sssata/HYKU/CAD/cad exports/008 UPPER ARM PCB2.DXF

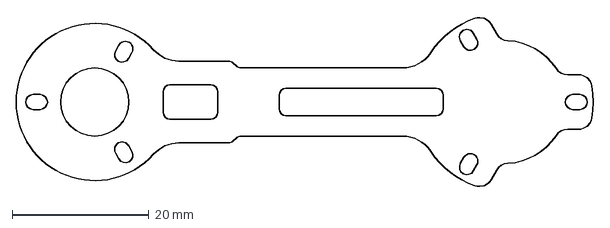
[picture p23: CAD file, 2021-12-31]
CAD/cad exports/008 UPPER ARM PCB2.DXF
84.6 x 25.1 mm
