sssata/HYKU/CAD/imported/Cherry MX Pins.SLDPRT

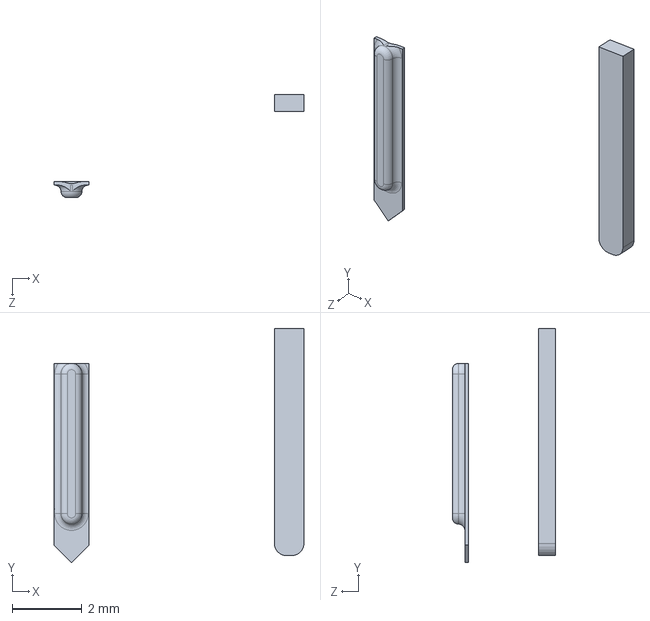
[picture p24: CAD file, 2021-12-25]
CAD/imported/Cherry MX Pins.SLDPRT
7.15 x 6.70 x 2.96 mm
