sssata/HYKU/CAD/006 BEARING MALE PLATE.SLDPRT

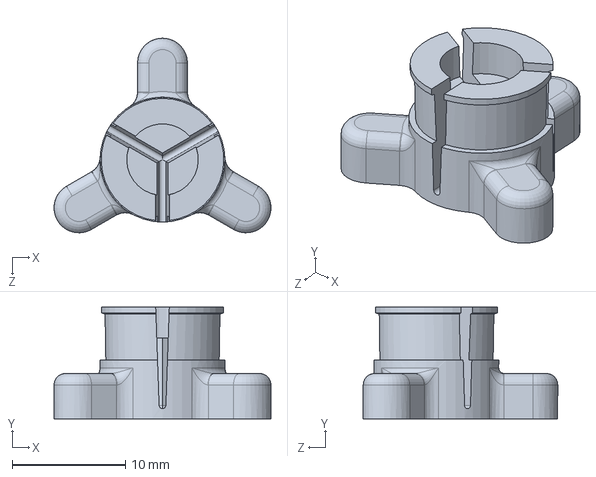
[picture p25: CAD file, 2022-01-21]
CAD/006 BEARING MALE PLATE.SLDPRT
19.1 x 9.85 x 17.2 mm
