sssata/HYKU/CAD/016 LOWER ARM PCB.SLDPRT

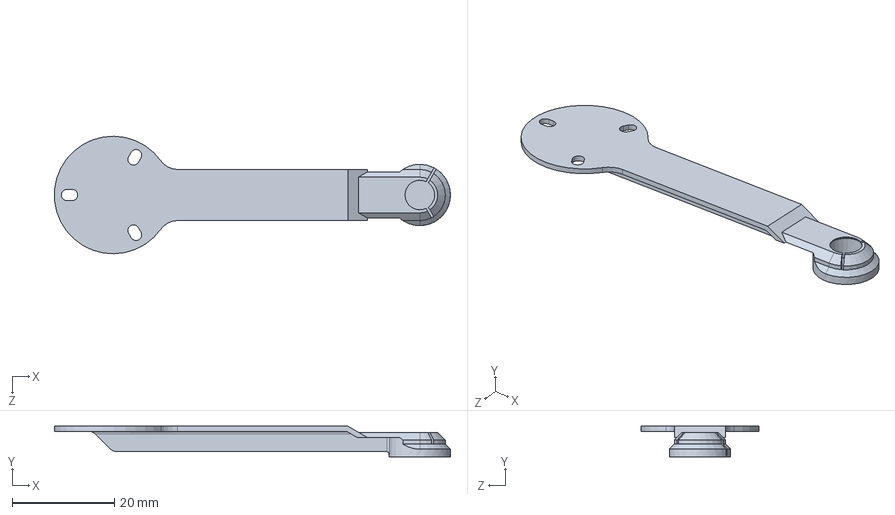
[picture p26: CAD file, 2022-01-21]
CAD/016 LOWER ARM PCB.SLDPRT
77.4 x 6.00 x 23.0 mm
