sssata/HYKU/CAD/imported/Cherry MX Stem.SLDPRT

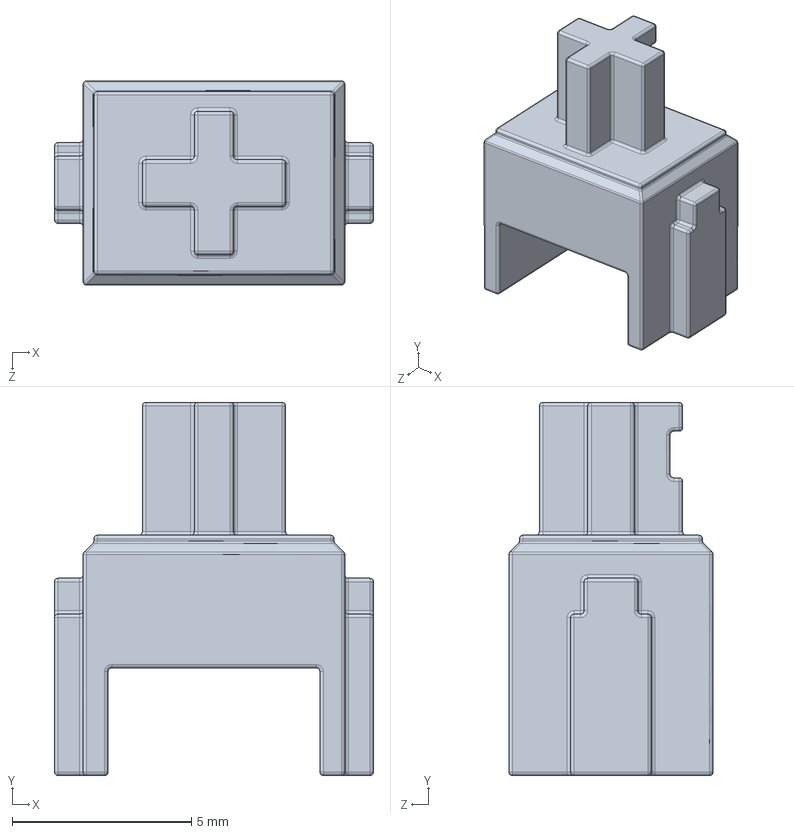
[picture p27: CAD file, 2021-12-25]
CAD/imported/Cherry MX Stem.SLDPRT
8.90 x 10.4 x 5.70 mm
