sssata/HYKU/CAD/imported/Cherry MX Top Housing.SLDPRT

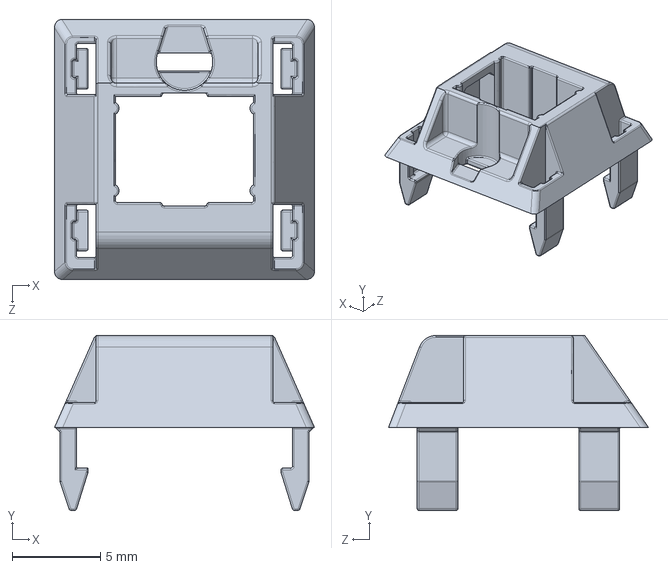
[picture p28: CAD file, 2021-12-25]
CAD/imported/Cherry MX Top Housing.SLDPRT
14.7 x 9.90 x 14.7 mm
