sssata/HYKU/CAD/008 UPPER ARM PCB.SLDPRT

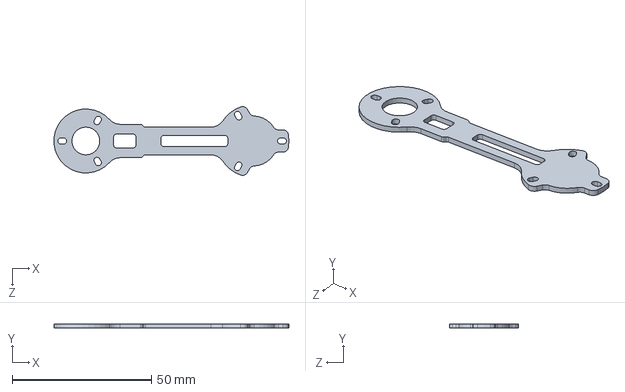
[picture p29: CAD file, 2021-12-31]
CAD/008 UPPER ARM PCB.SLDPRT
84.4 x 1.60 x 24.7 mm
