sssata/HYKU/CAD/imported/Cherry MX LED.SLDPRT

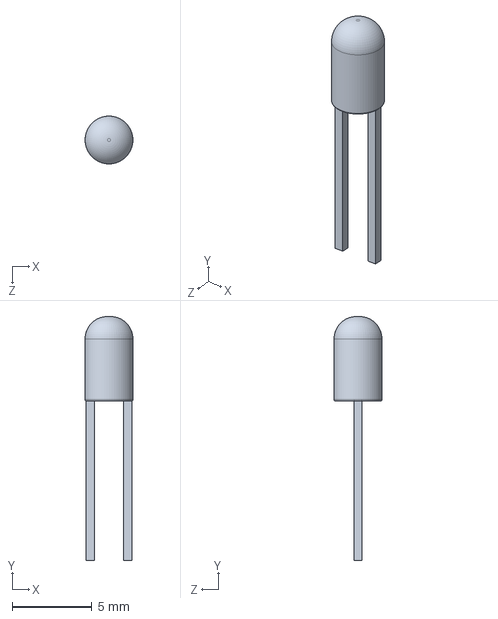
[picture p30: CAD file, 2021-12-25]
CAD/imported/Cherry MX LED.SLDPRT
3.00 x 15.3 x 3.00 mm
