sssata/HYKU/CAD/022 PEN NIB.SLDPRT

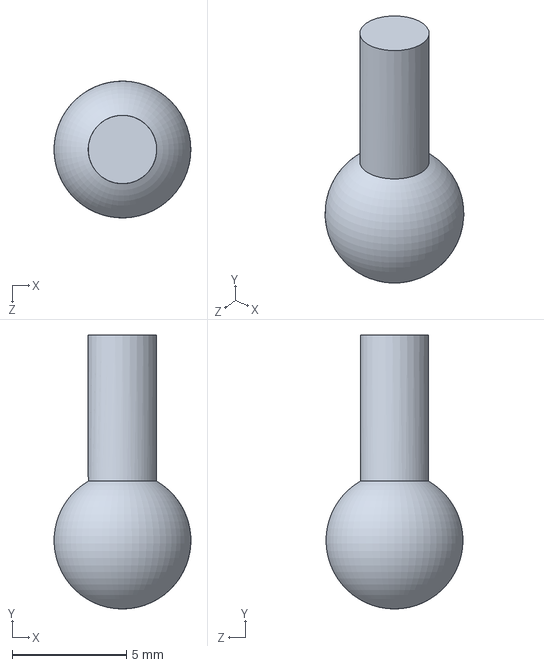
[picture p31: CAD file, 2021-12-31]
CAD/022 PEN NIB.SLDPRT
5.99 x 12.0 x 5.99 mm
