sssata/HYKU/CAD/010 BASE KICAD EXP.SLDPRT

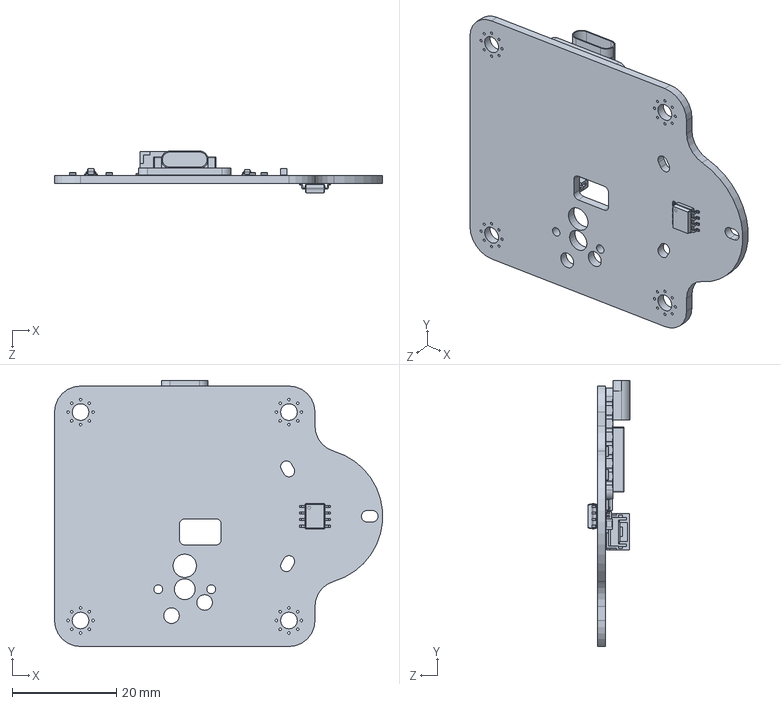
[picture p32: CAD file, 2021-12-31]
CAD/010 BASE KICAD EXP.SLDPRT
63.0 x 51.1 x 8.05 mm
