sssata/HYKU/CAD/013 AS5600 SOIC-8.SLDPRT

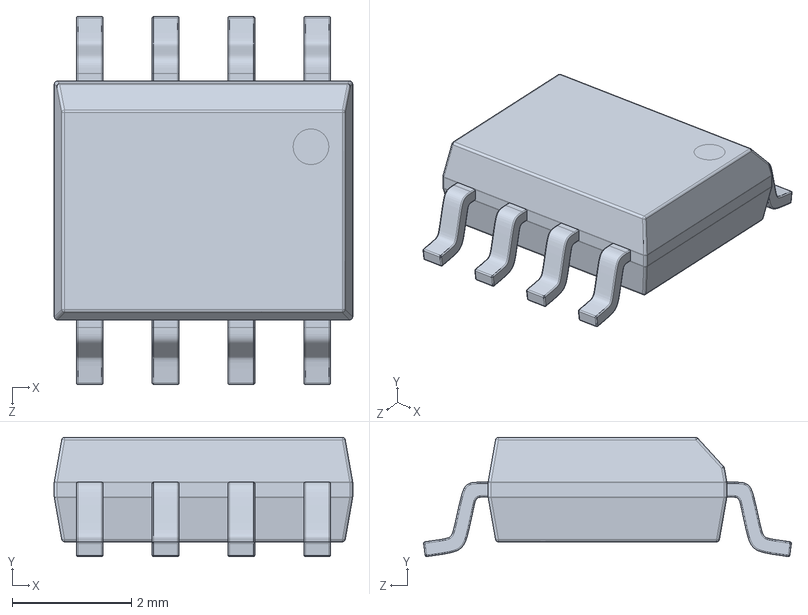
[picture p33: CAD file, 2021-12-31]
CAD/013 AS5600 SOIC-8.SLDPRT
5.00 x 2.00 x 6.16 mm
