sssata/HYKU/CAD/005 BEARING FEMALE PLATE.SLDPRT

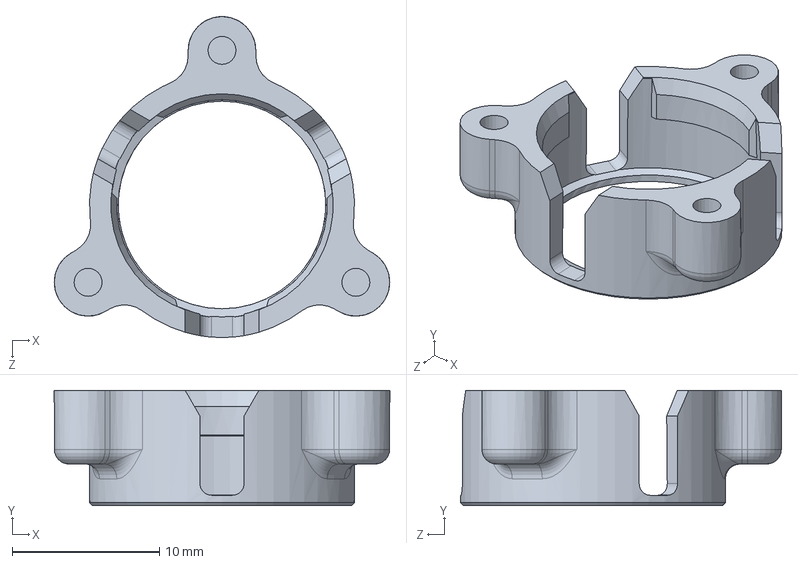
[picture p34: CAD file, 2021-12-31]
CAD/005 BEARING FEMALE PLATE.SLDPRT
22.8 x 7.82 x 21.8 mm
