sssata/HYKU/CAD/009 6x2mm MAGNET.SLDPRT

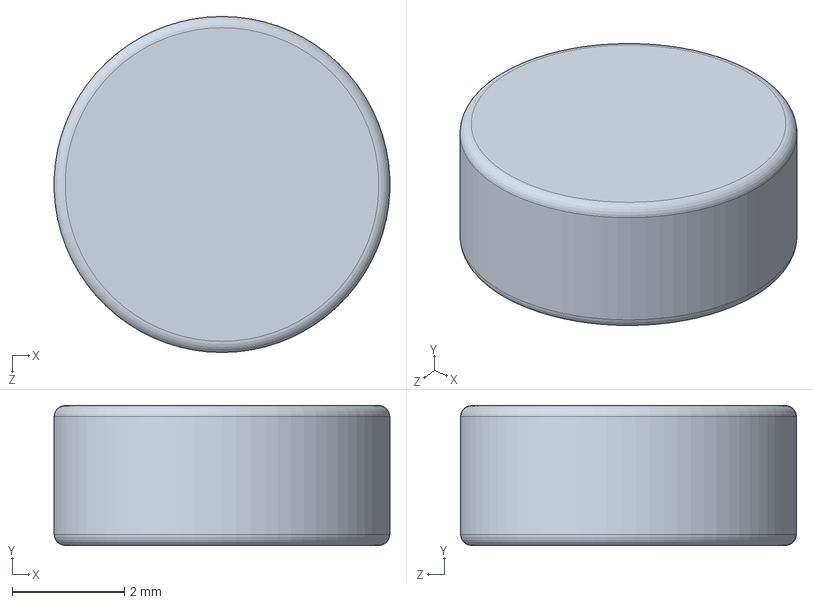
[picture p35: CAD file, 2021-12-31]
CAD/009 6x2mm MAGNET.SLDPRT
5.99 x 2.50 x 6.00 mm
