sssata/HYKU/CAD/017 AREA PCB.SLDPRT

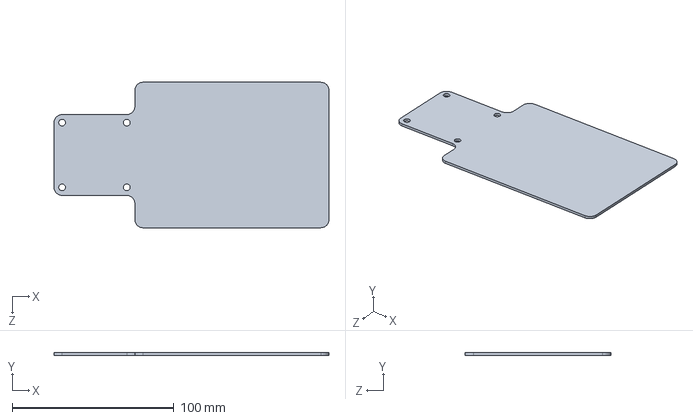
[picture p36: CAD file, 2021-12-25]
CAD/017 AREA PCB.SLDPRT
170.0 x 1.60 x 90.0 mm
