sssata/HYKU/CAD/003 LOWER ARM REV2.SLDPRT

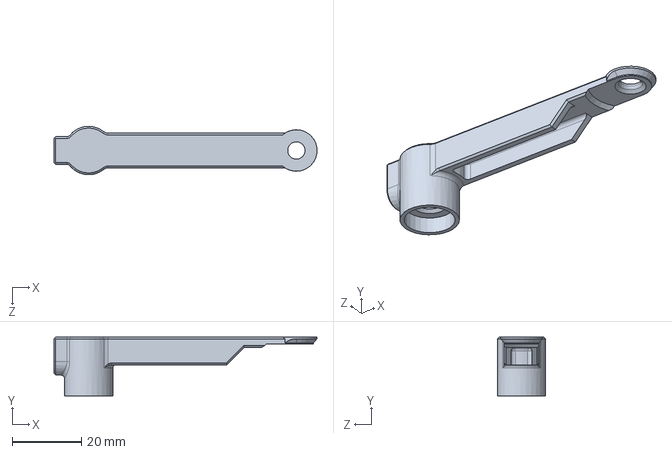
[picture p37: CAD file, 2021-12-25]
CAD/003 LOWER ARM REV2.SLDPRT
76.0 x 17.0 x 14.0 mm
