sssata/HYKU/CAD/015 JST NSH 5 PIN WIRE SIDE.SLDPRT

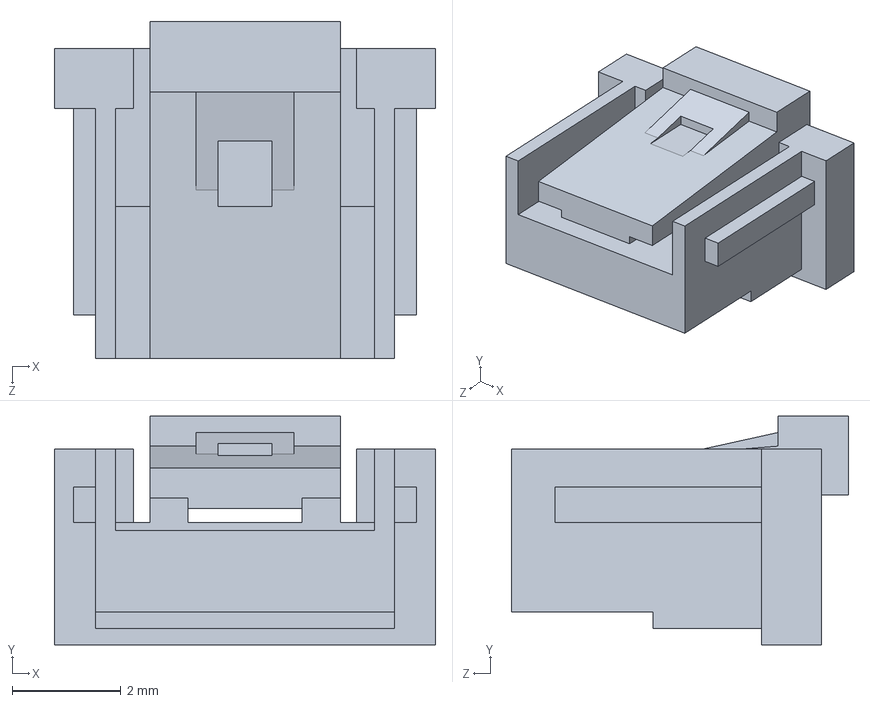
[picture p38: CAD file, 2021-12-25]
CAD/015 JST NSH 5 PIN WIRE SIDE.SLDPRT
7.00 x 4.20 x 6.20 mm
