sssata/HYKU/CAD/002 UPPER ARM REV2.SLDPRT

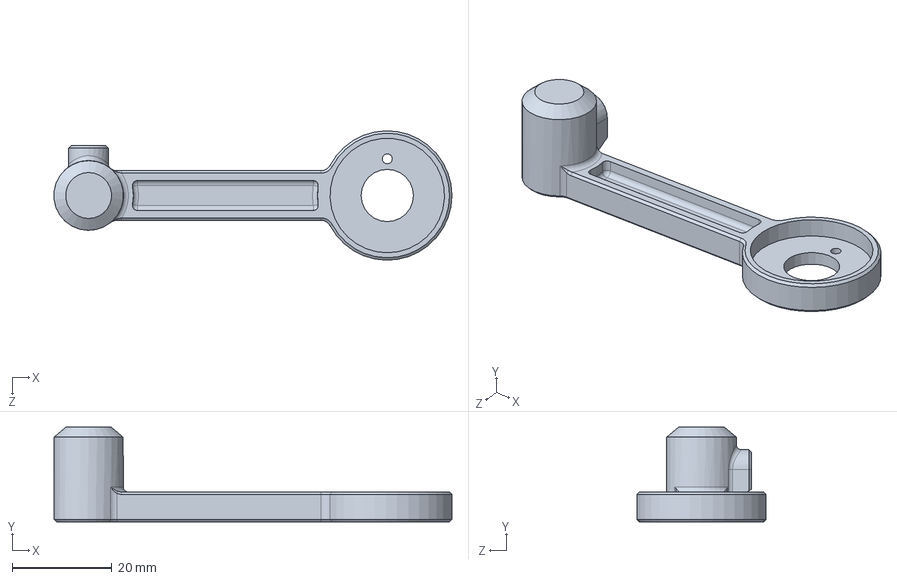
[picture p39: CAD file, 2021-12-25]
CAD/002 UPPER ARM REV2.SLDPRT
80.0 x 19.0 x 26.0 mm
