sssata/HYKU/CAD/001 BASE REV2.SLDPRT

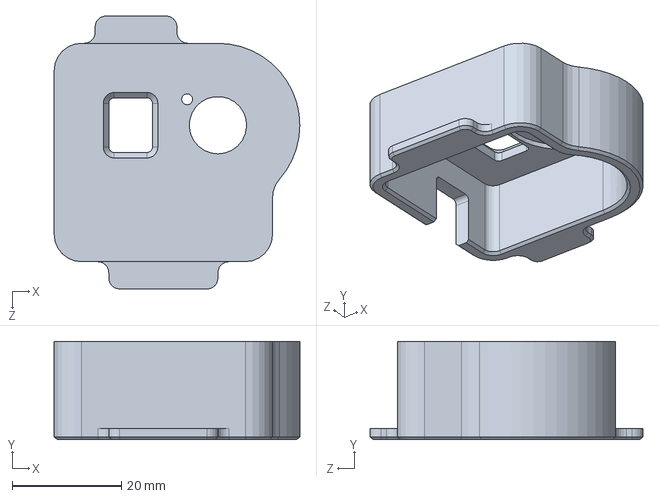
[picture p40: CAD file, 2021-12-25]
CAD/001 BASE REV2.SLDPRT
45.0 x 18.0 x 50.0 mm
