sssata/HYKU/CAD/007 6700ZZ bearing.SLDPRT

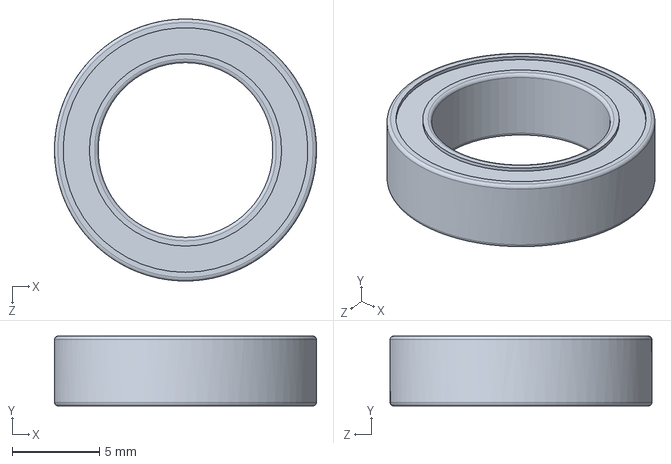
[picture p41: CAD file, 2021-12-25]
CAD/007 6700ZZ bearing.SLDPRT
15.0 x 4.00 x 15.0 mm
