sssata/HYKU/CAD/010 BASE.SLDPRT

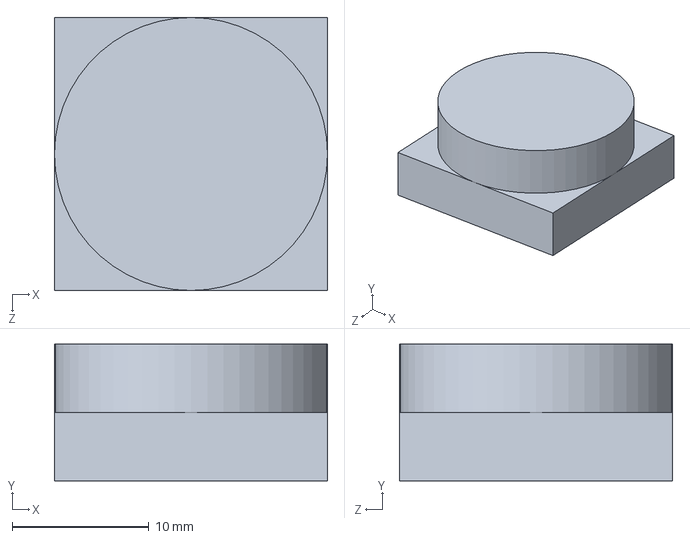
[picture p42: CAD file, 2021-12-25]
CAD/010 BASE.SLDPRT
20.0 x 10.0 x 20.0 mm
