sssata/HYKU/CAD/012 SeeeduinoXiao3D.SLDPRT

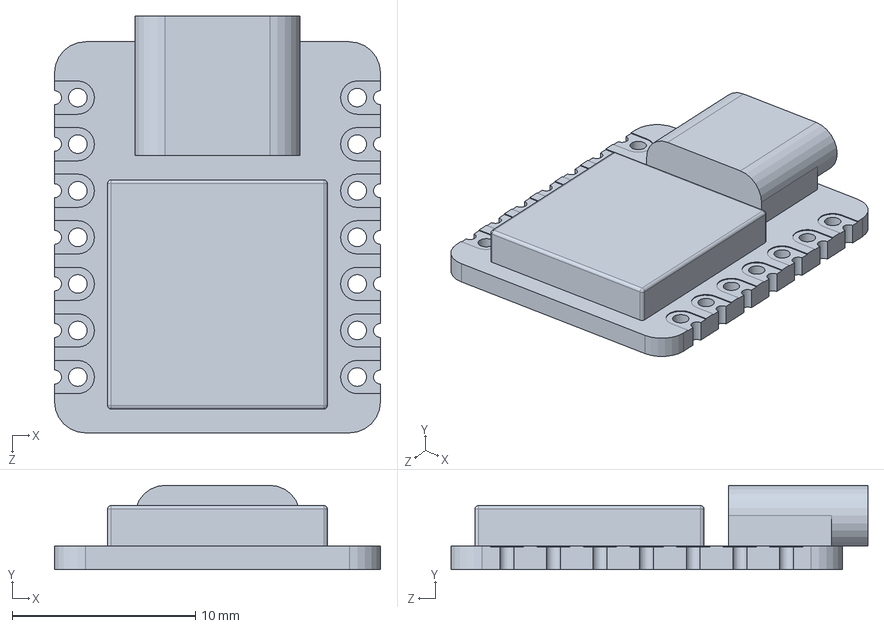
[picture p43: CAD file, 2021-12-25]
CAD/012 SeeeduinoXiao3D.SLDPRT
17.8 x 4.60 x 22.7 mm
