sssata/HYKU/CAD/004 MR85ZZ bearing.SLDPRT

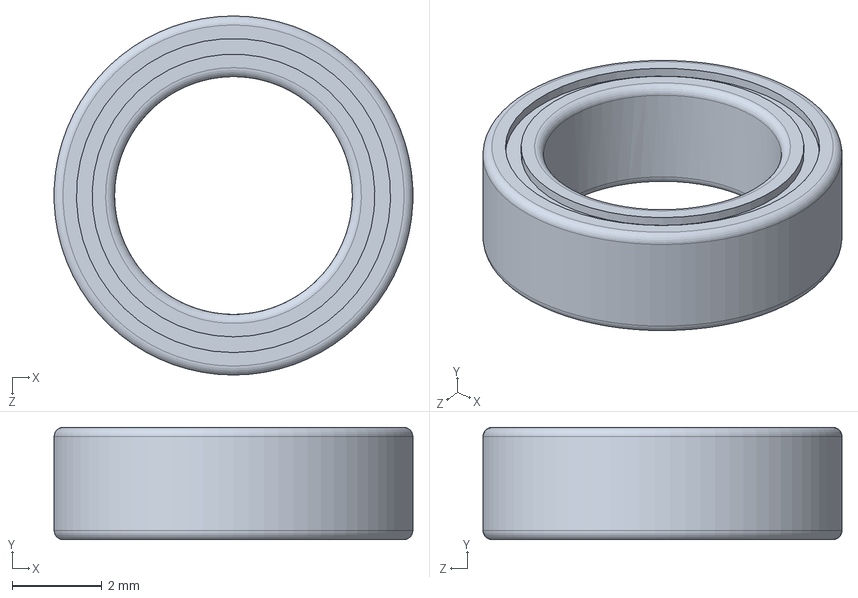
[picture p44: CAD file, 2021-12-25]
CAD/004 MR85ZZ bearing.SLDPRT
7.99 x 2.50 x 8.00 mm
