sssata/HYKU/CAD/011 BASE PCB.SLDPRT

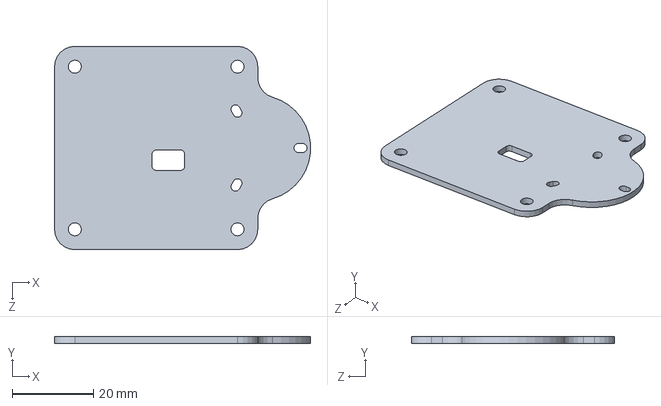
[picture p45: CAD file, 2021-12-25]
CAD/011 BASE PCB.SLDPRT
63.0 x 1.60 x 50.0 mm
