sssata/HYKU/CAD/020 STANDOFF 3x6.SLDPRT

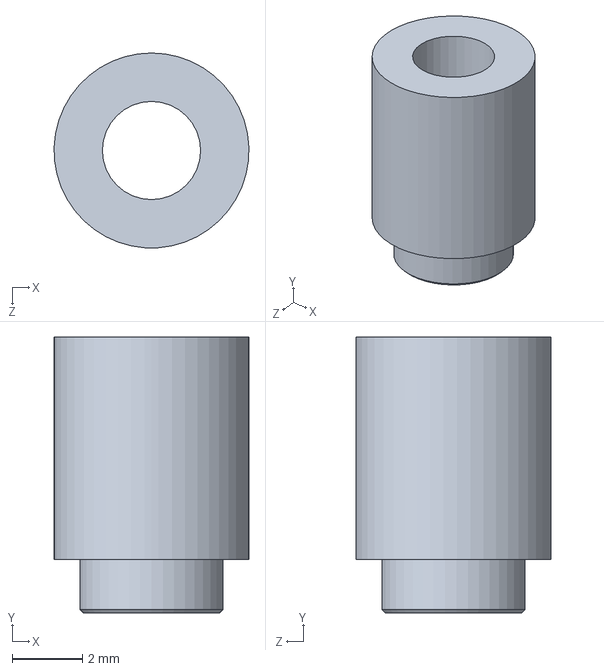
[picture p46: CAD file, 2021-12-25]
CAD/020 STANDOFF 3x6.SLDPRT
5.56 x 7.87 x 5.56 mm
