sssata/HYKU/CAD/019.SLDPRT

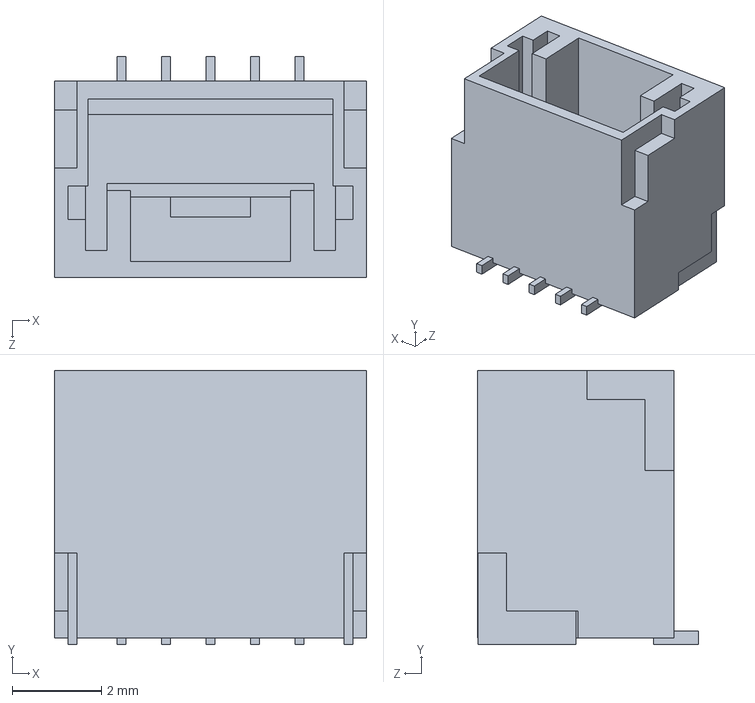
[picture p47: CAD file, 2021-12-25]
CAD/019.SLDPRT
7.00 x 6.15 x 4.95 mm
