sssata/HYKU/CAD/014 JST NSH 5 PIN BOARD SIDE.SLDPRT

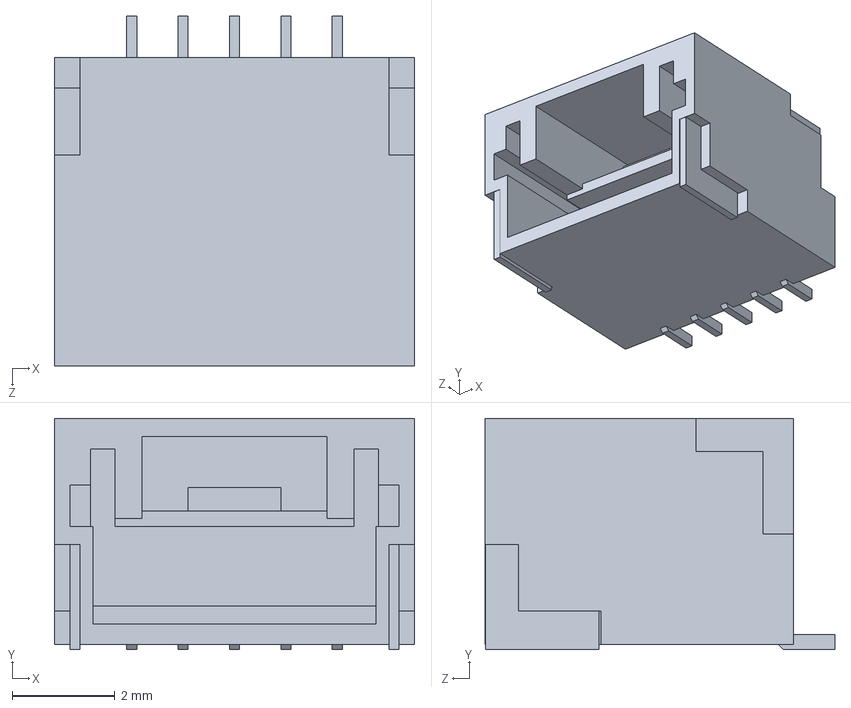
[picture p48: CAD file, 2021-12-25]
CAD/014 JST NSH 5 PIN BOARD SIDE.SLDPRT
7.00 x 4.50 x 6.80 mm
