sssata/HYKU/CAD/020 JST NSH CRIMP.SLDPRT

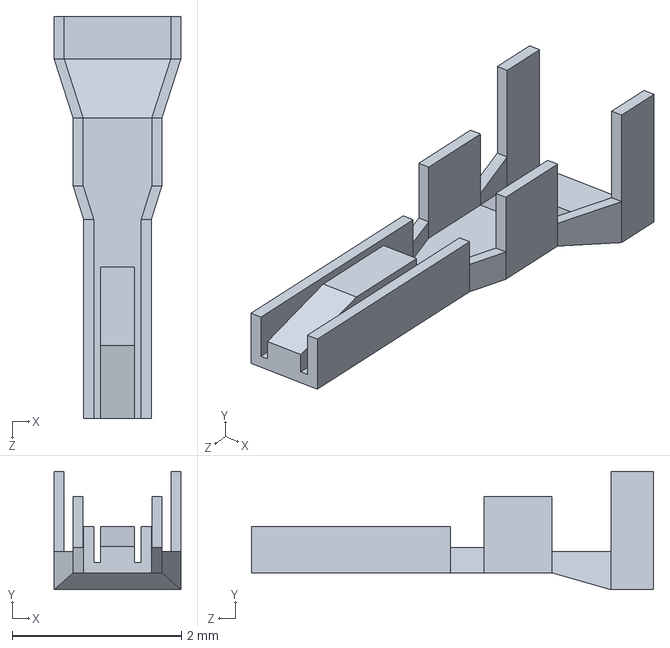
[picture p49: CAD file, 2021-12-25]
CAD/020 JST NSH CRIMP.SLDPRT
1.50 x 1.40 x 4.75 mm
