sssata/HYKU/python/calibrate_image_annotated.png

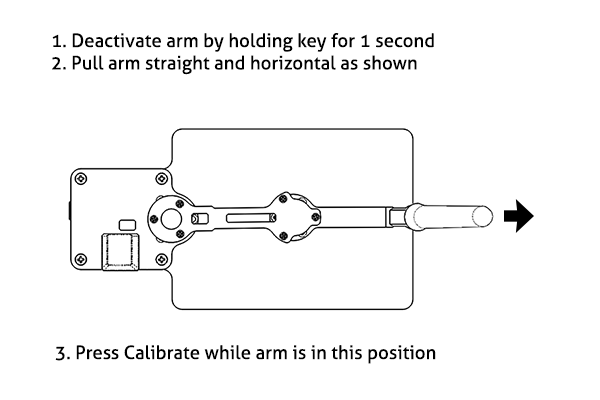
python/calibrate_image_annotated.png
